gitRaksha/SmartVest_Project/Images/Capture d'écran 2025-05-01 123604.png

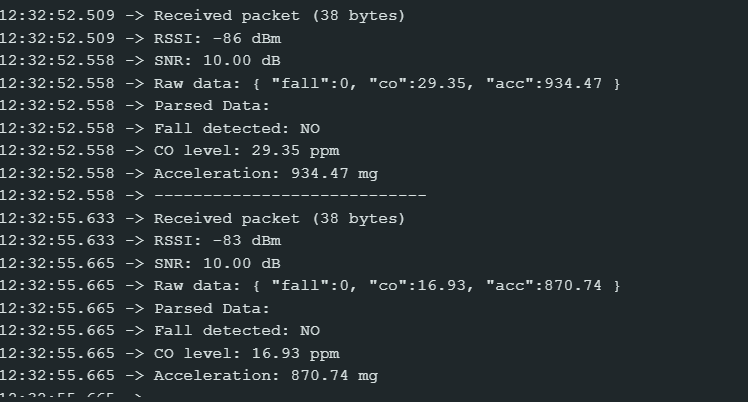
Images/Capture d'écran 2025-05-01 123604.png
