gitRaksha/SmartVest_Project/Images/Capture d'écran 2025-05-04 211845.png

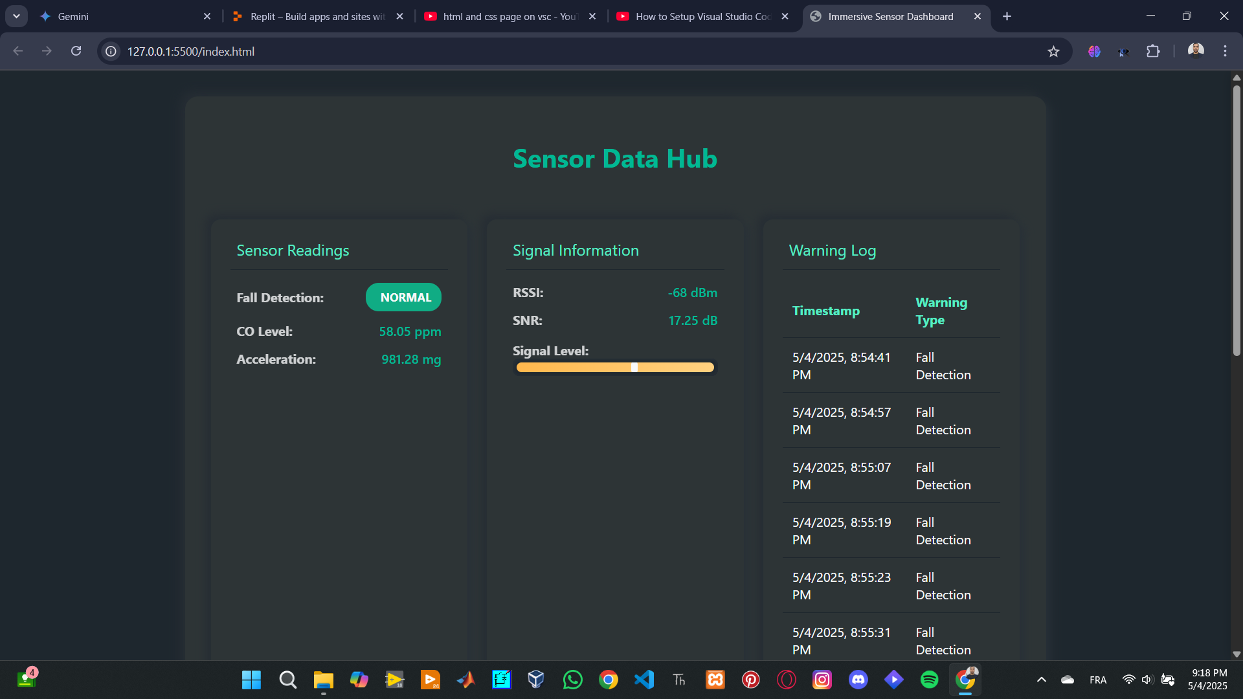
Images/Capture d'écran 2025-05-04 211845.png
