gitRaksha/SmartVest_Project/Images/Capture d'écran 2025-05-11 214654.png

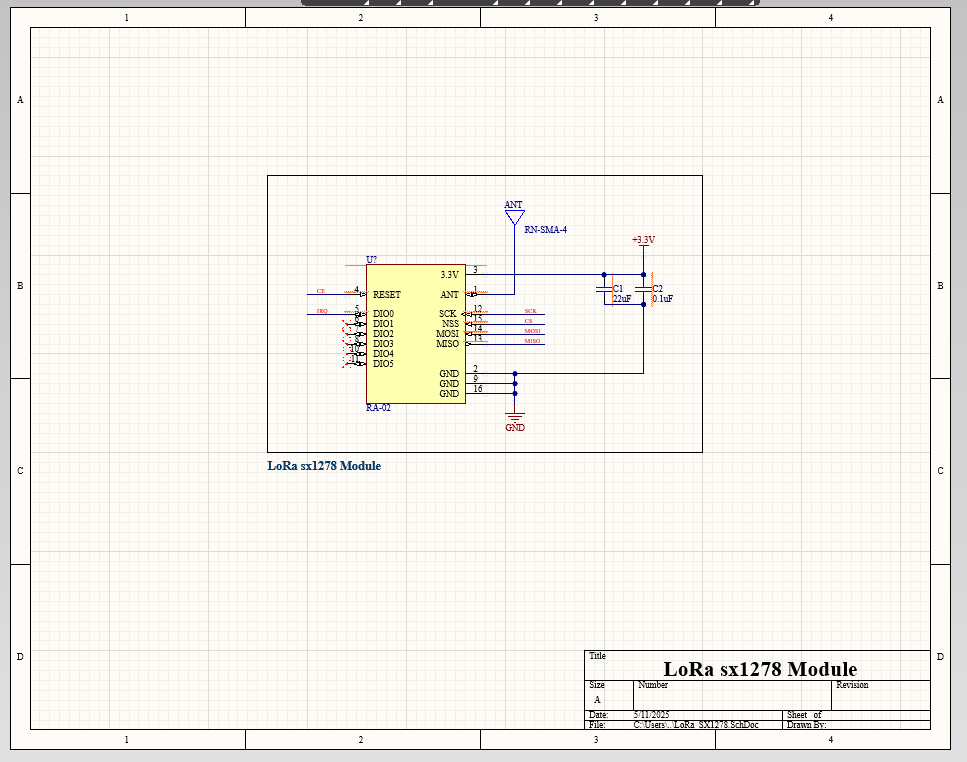
Images/Capture d'écran 2025-05-11 214654.png
