gitRaksha/SmartVest_Project/Images/Capture d'écran 2025-05-31 155221.png

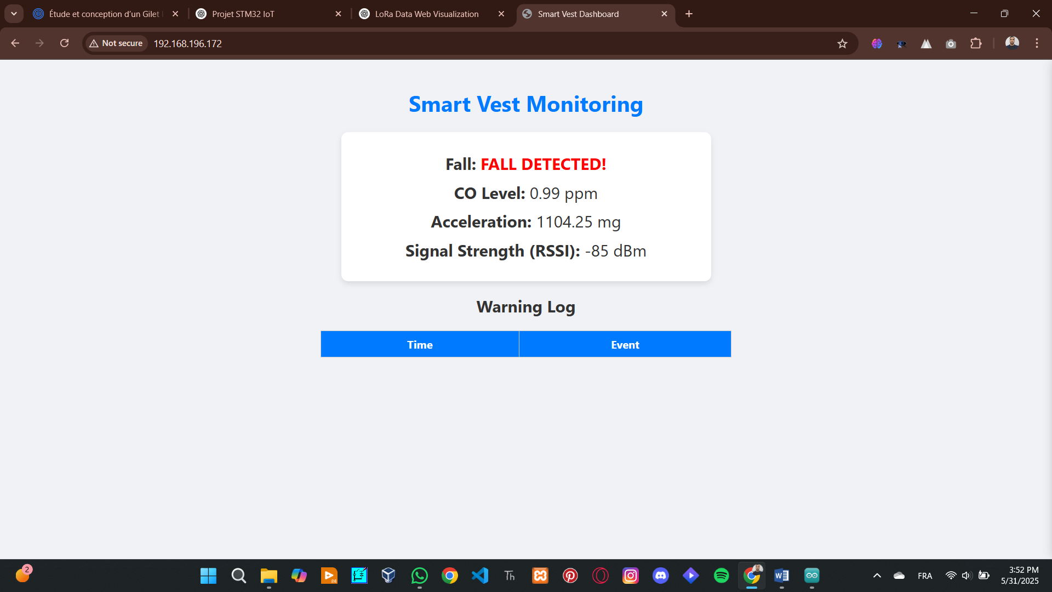
Images/Capture d'écran 2025-05-31 155221.png
