gitRaksha/SmartVest_Project/Images/Capture d'écran 2025-05-31 155903.png

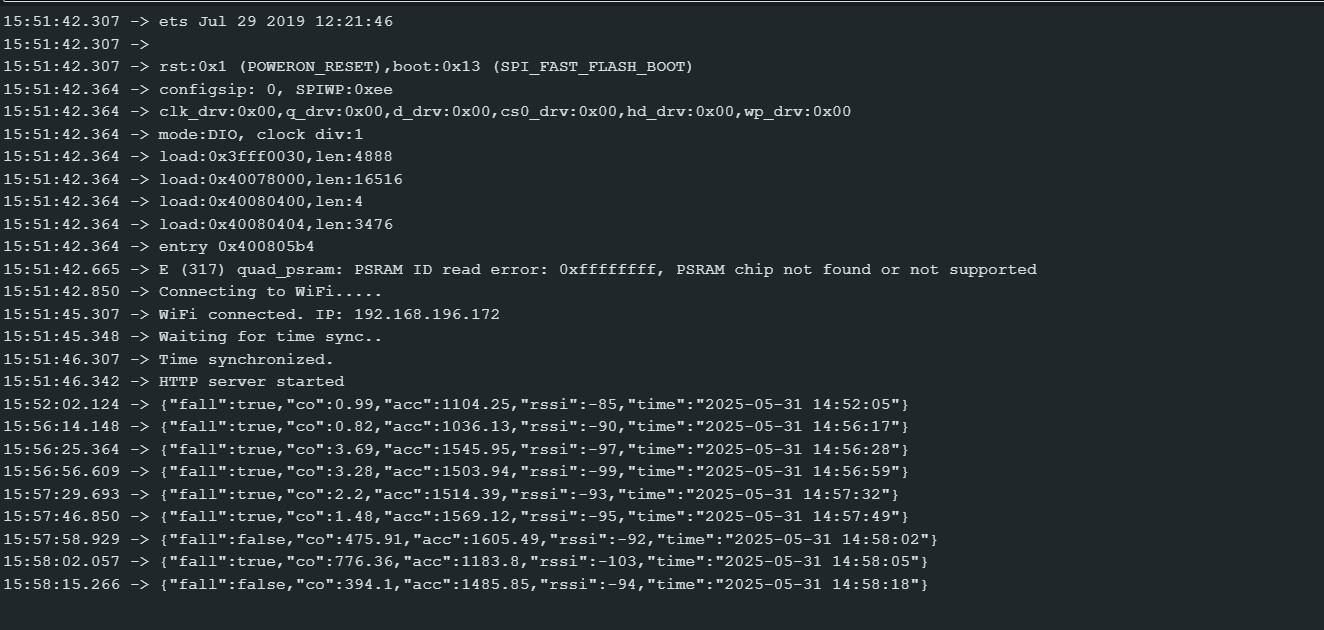
Images/Capture d'écran 2025-05-31 155903.png
