gitRaksha/SmartVest_Project/Images/Capture d'écran 2025-06-03 121555.png

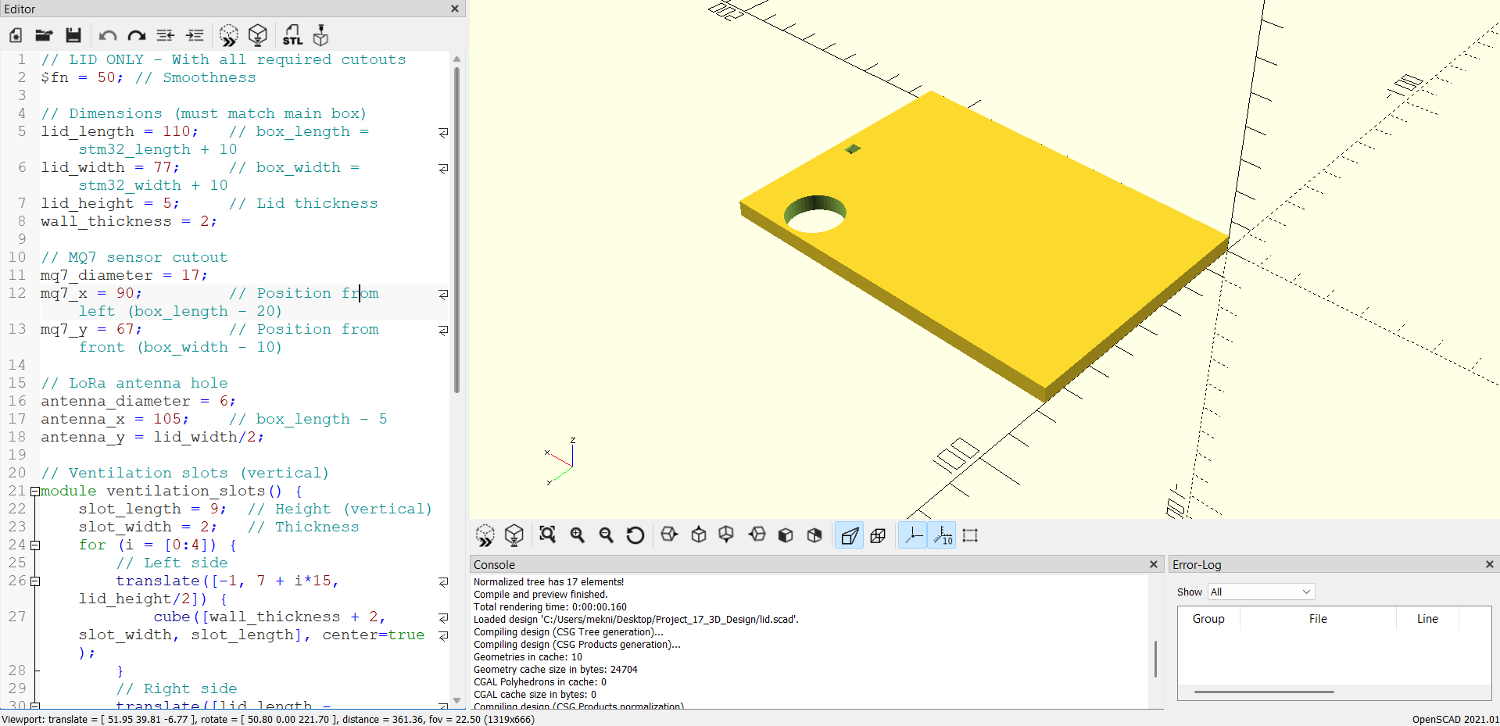
Images/Capture d'écran 2025-06-03 121555.png
