gitRaksha/SmartVest_Project/Images/WhatsApp Image 2025-05-24 à 20.48.16_56ef8105.jpg

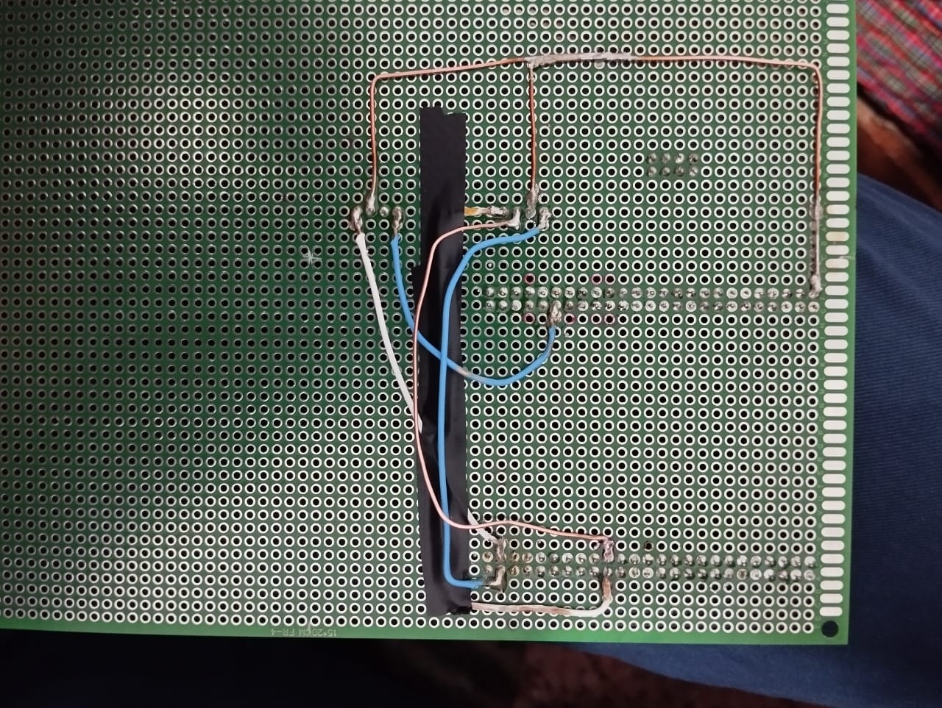
Images/WhatsApp Image 2025-05-24 à 20.48.16_56ef8105.jpg
